melatova/PlantHabitatMonitor/docs/hurricane_vase_cross_section.png

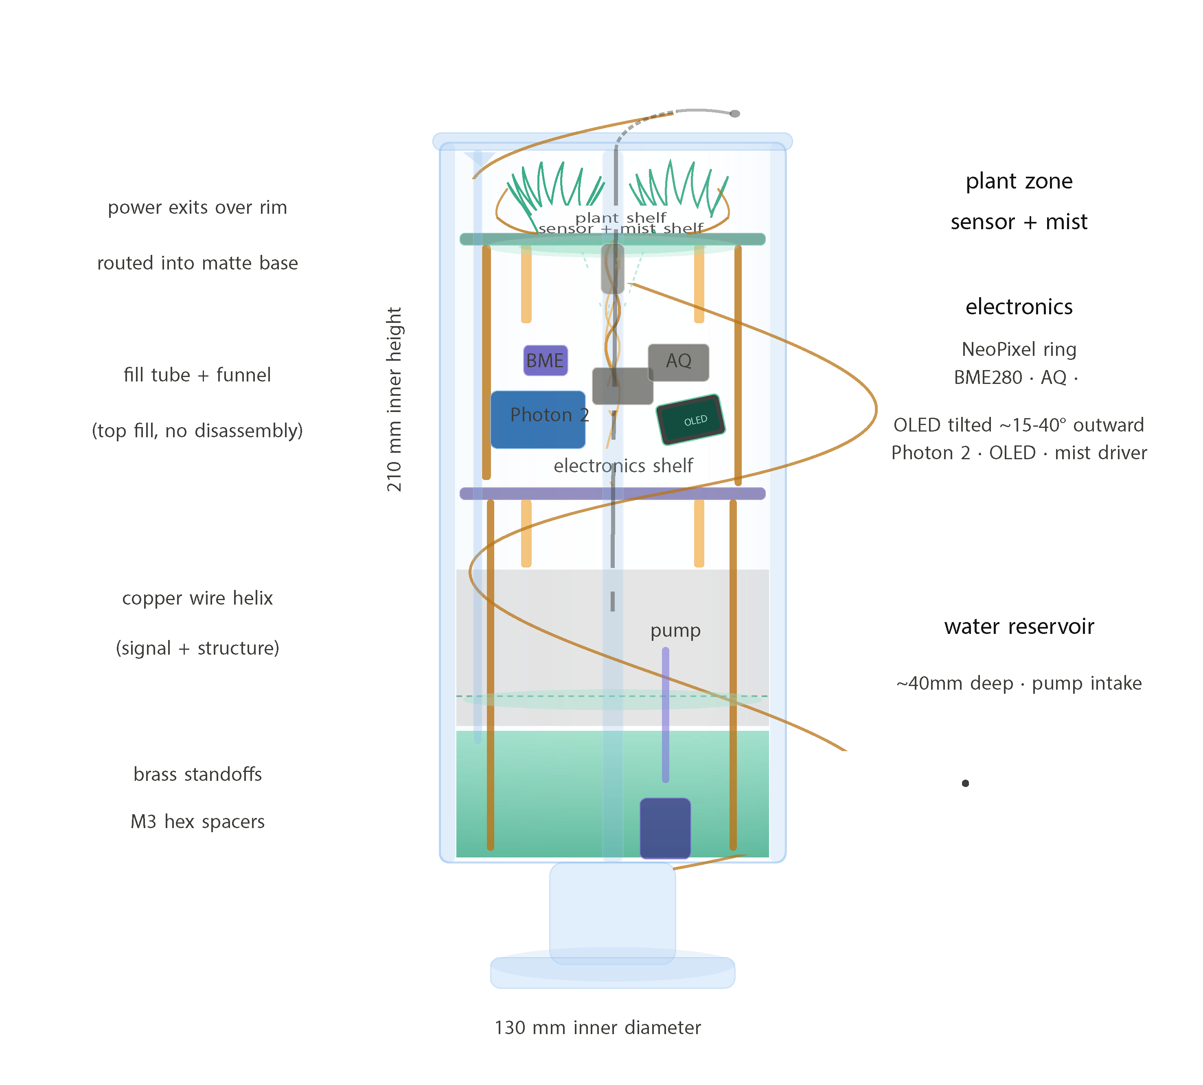
docs/hurricane_vase_cross_section.png
