melatova/PlantHabitatMonitor/docs/plantMonitorFritz_bb.png

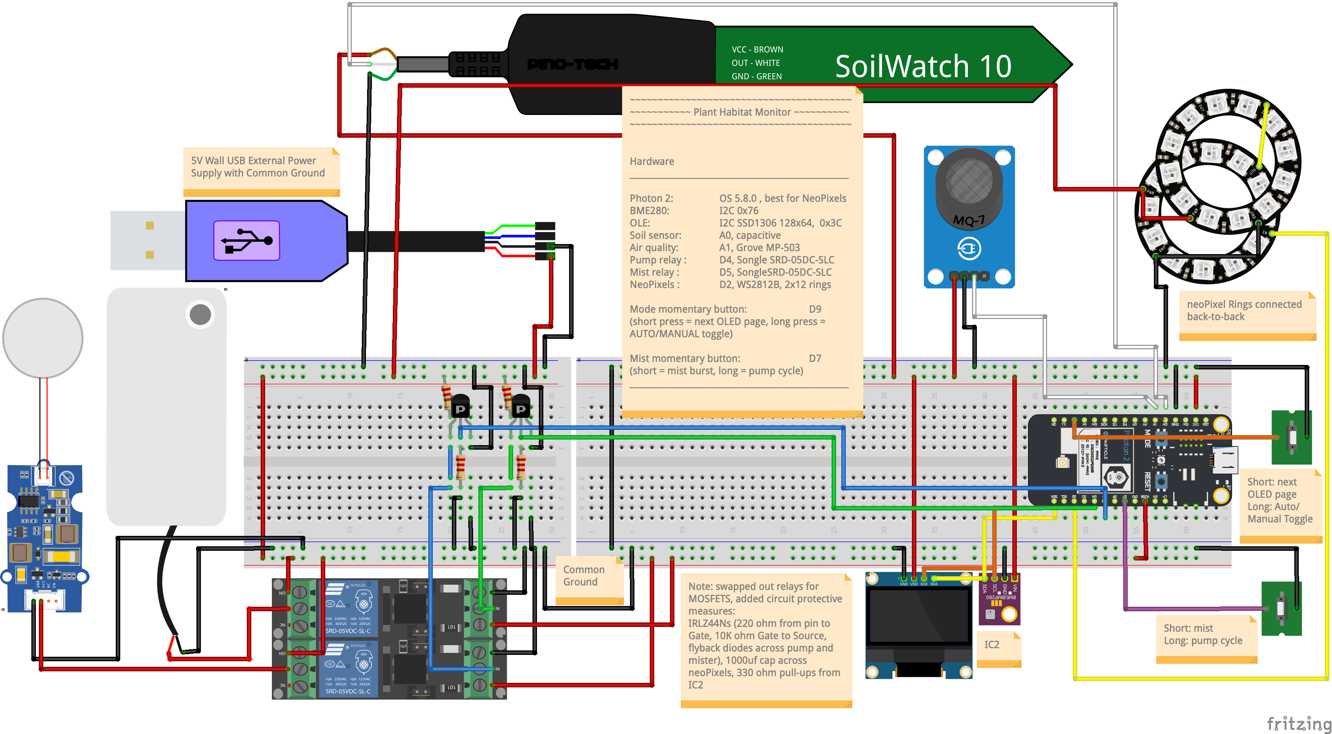
docs/plantMonitorFritz_bb.png
