melatova/PlantHabitatMonitor/docs/plantMonitorFritz_schem.png

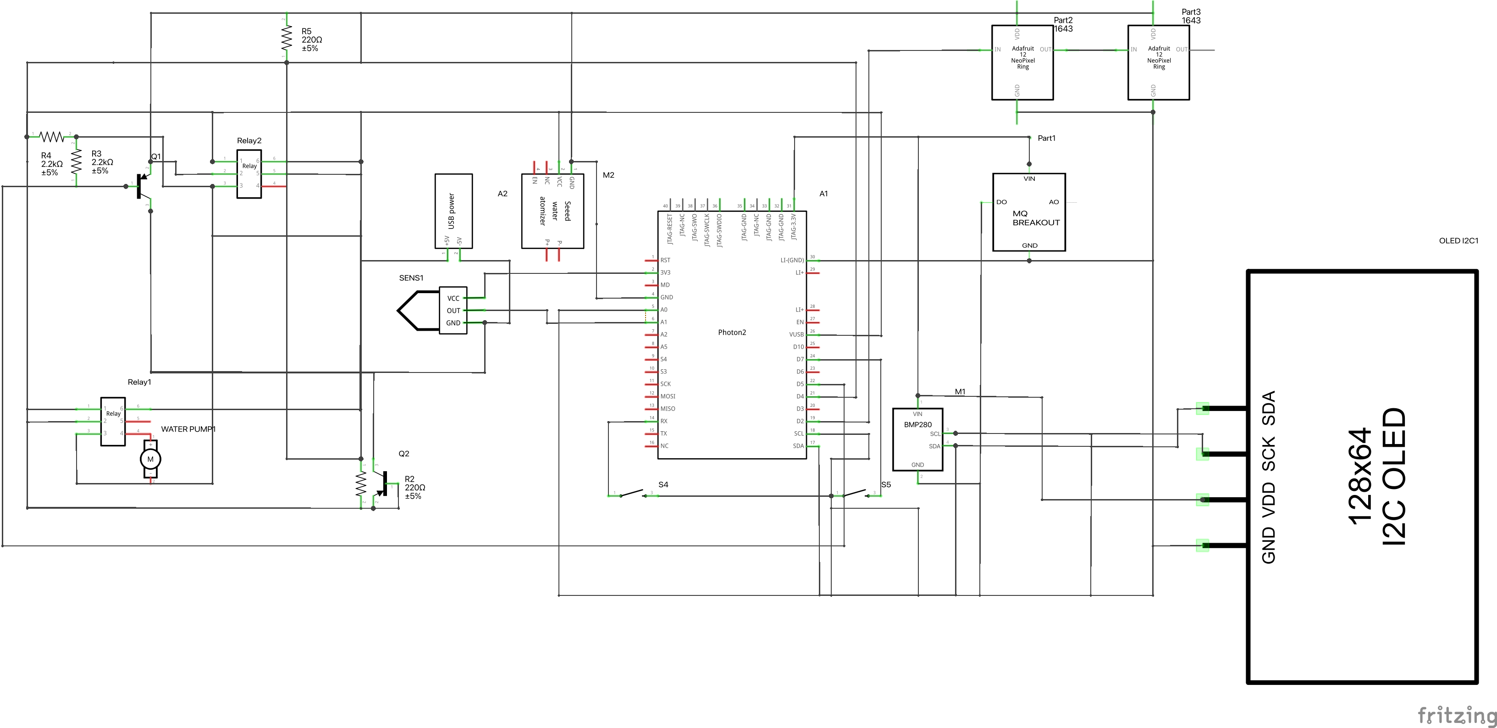
docs/plantMonitorFritz_schem.png
