melatova/PlantHabitatMonitor/images/Adafruit_Dashboard.png

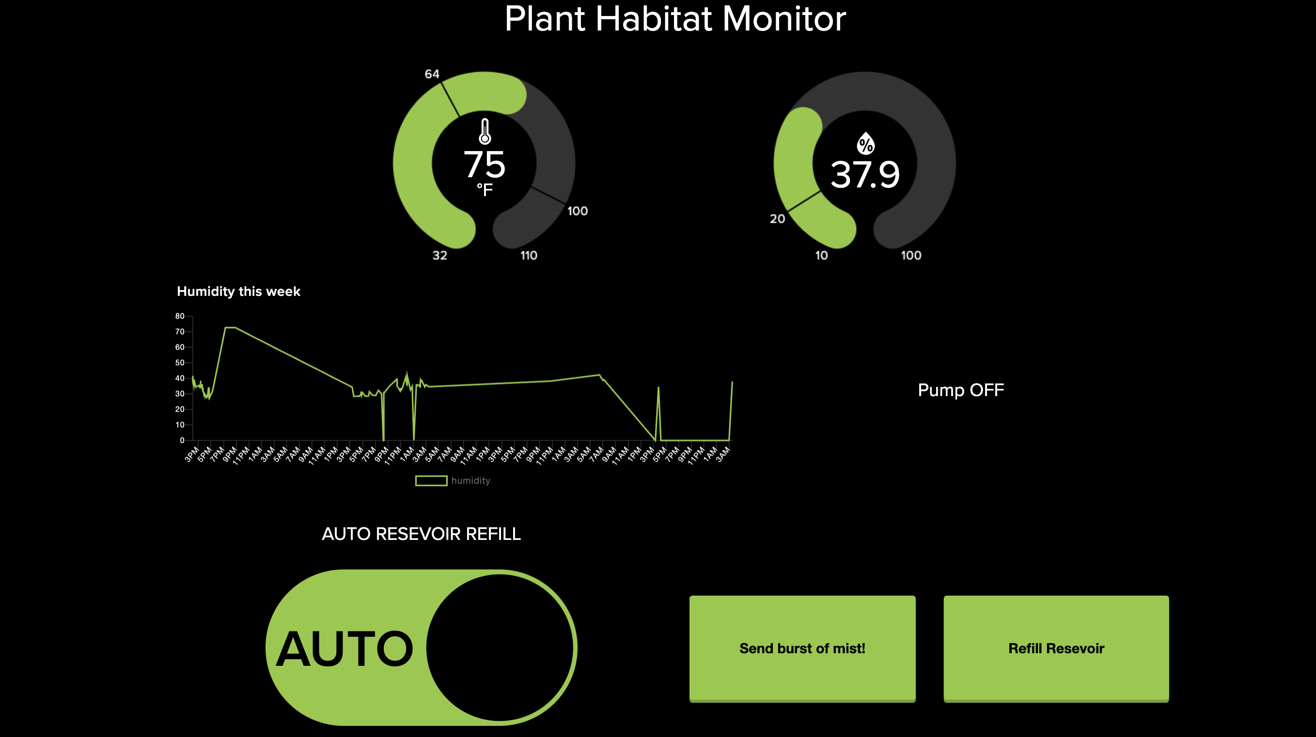
images/Adafruit_Dashboard.png
