melatova/PlantHabitatMonitor/images/Adafruit_Dashboard_Feeds.png

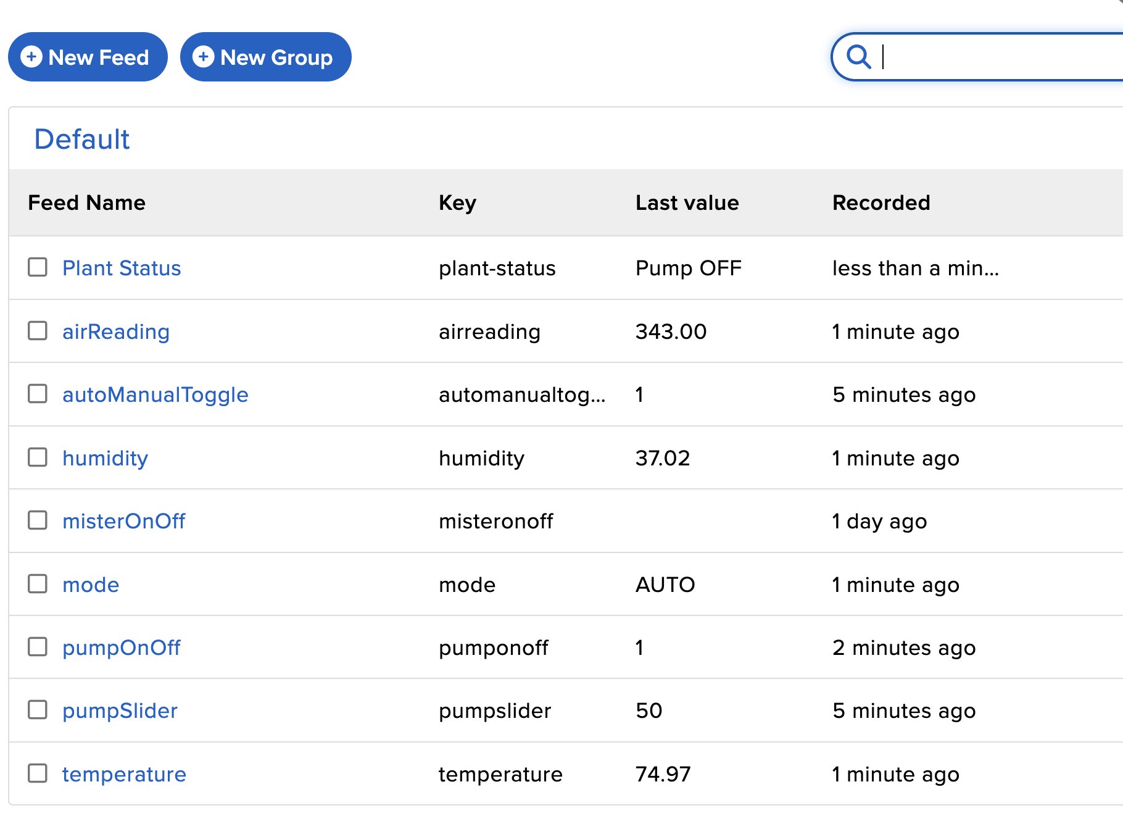
images/Adafruit_Dashboard_Feeds.png
