melatova/PlantHabitatMonitor/images/Air_plant_sanctuary_1.png

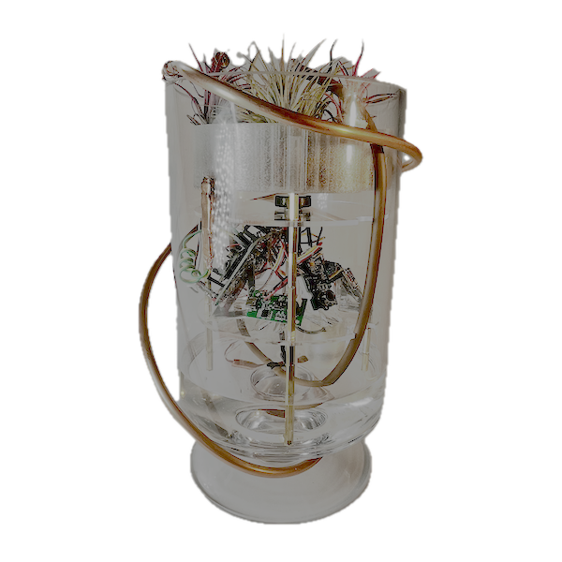
images/Air_plant_sanctuary_1.png
