melatova/PlantHabitatMonitor/images/Air_plant_sanctuary_med.gif

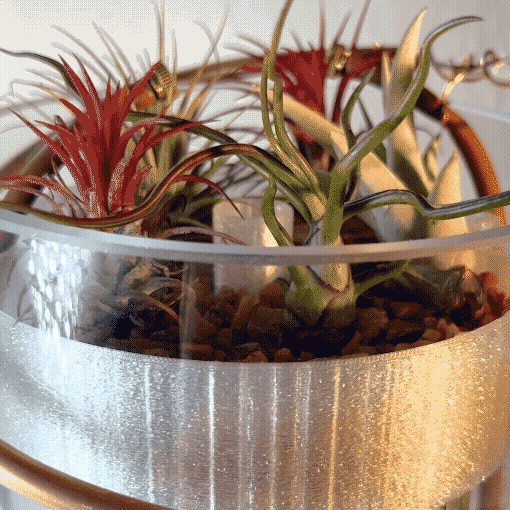
images/Air_plant_sanctuary_med.gif
