melatova/PlantHabitatMonitor/images/airplantPot_misted.png

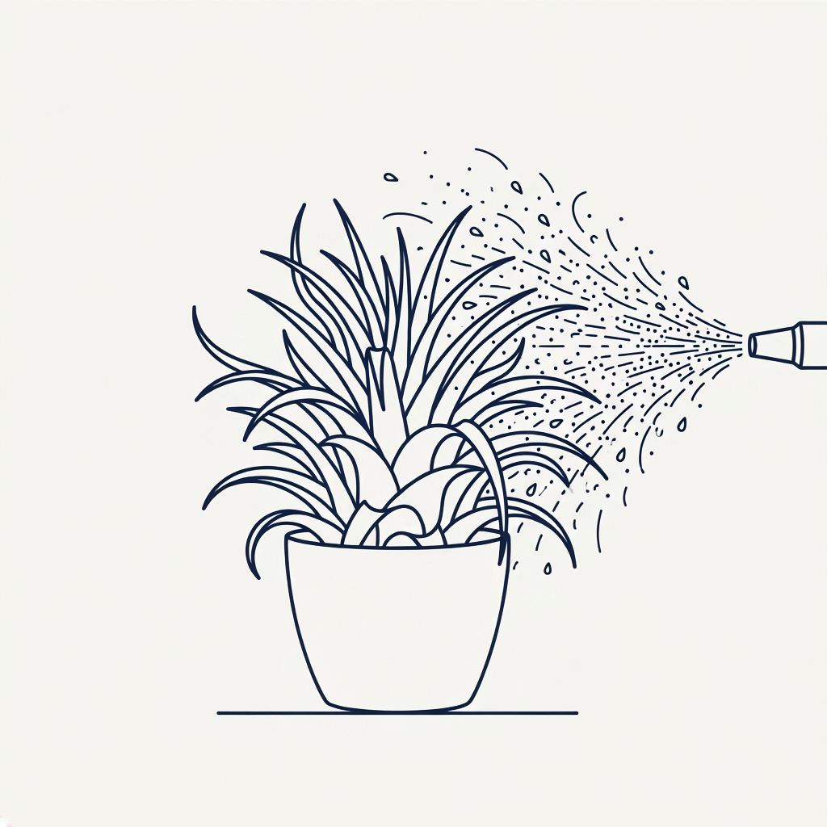
images/airplantPot_misted.png
