melatova/PlantHabitatMonitor/images/arranging_laser_cut_board_stands_sm.png

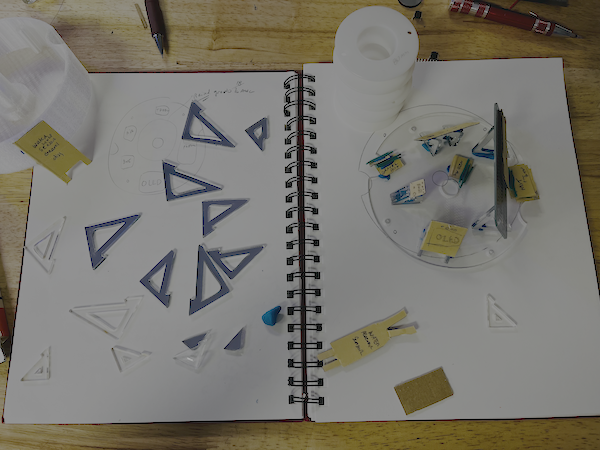
images/arranging_laser_cut_board_stands_sm.png
