melatova/PlantHabitatMonitor/images/breadboard_with_relays_sm.png

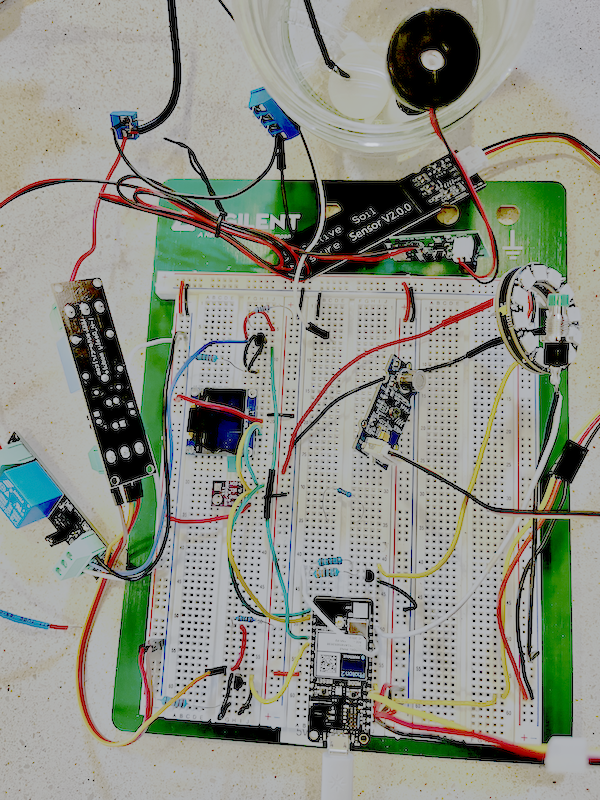
images/breadboard_with_relays_sm.png
