melatova/PlantHabitatMonitor/images/Hurricane_vase_on_snare_for_scale_sm.png

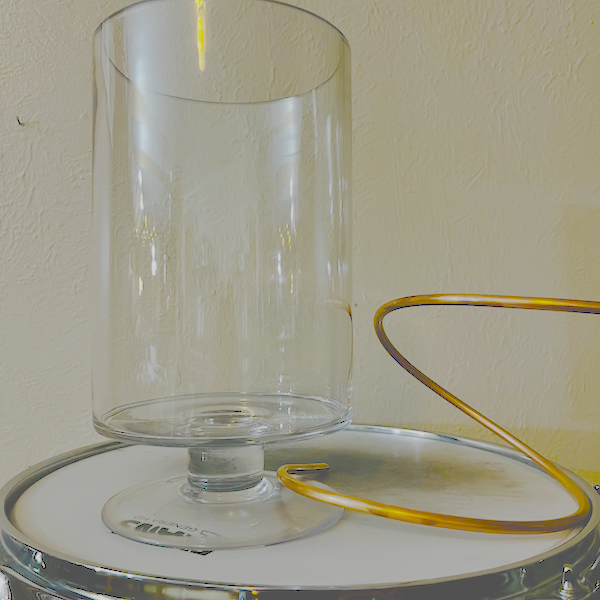
images/Hurricane_vase_on_snare_for_scale_sm.png
