melatova/PlantHabitatMonitor/images/Piezo_atomizer_board_TD-002-DIY-back.png

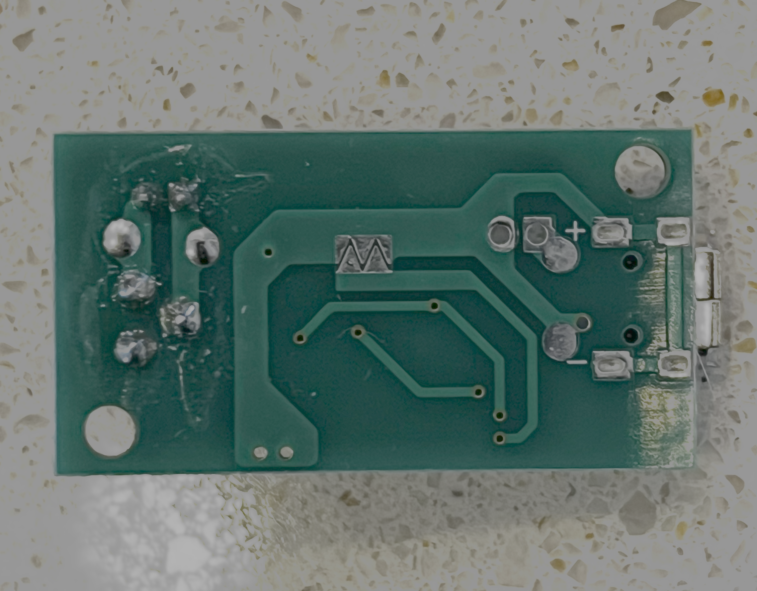
images/Piezo_atomizer_board_TD-002-DIY-back.png
