melatova/PlantHabitatMonitor/images/piezo_atomizer_magnified.png

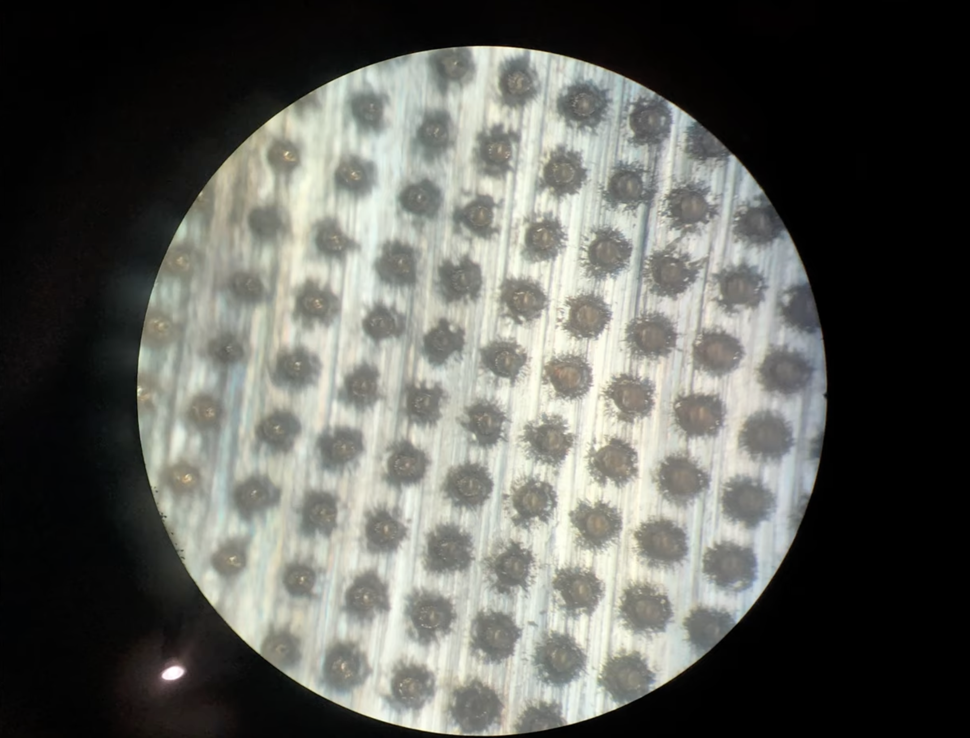
images/piezo_atomizer_magnified.png
