melatova/PlantHabitatMonitor/images/planning_circuit_layer_arrangment_sm.png

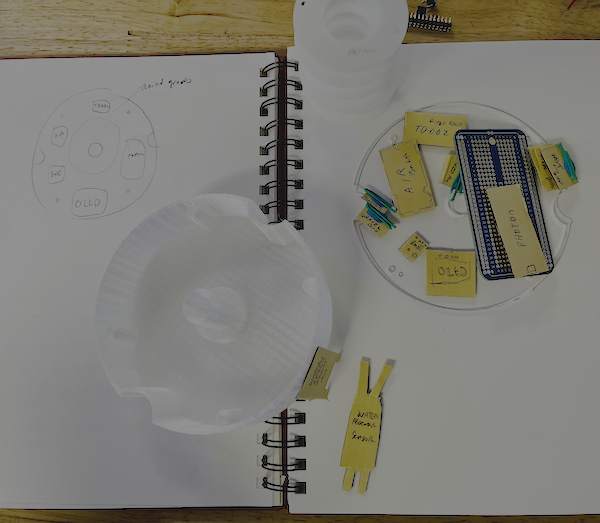
images/planning_circuit_layer_arrangment_sm.png
