melatova/PlantHabitatMonitor/images/PlantHabitatMonitor01.png

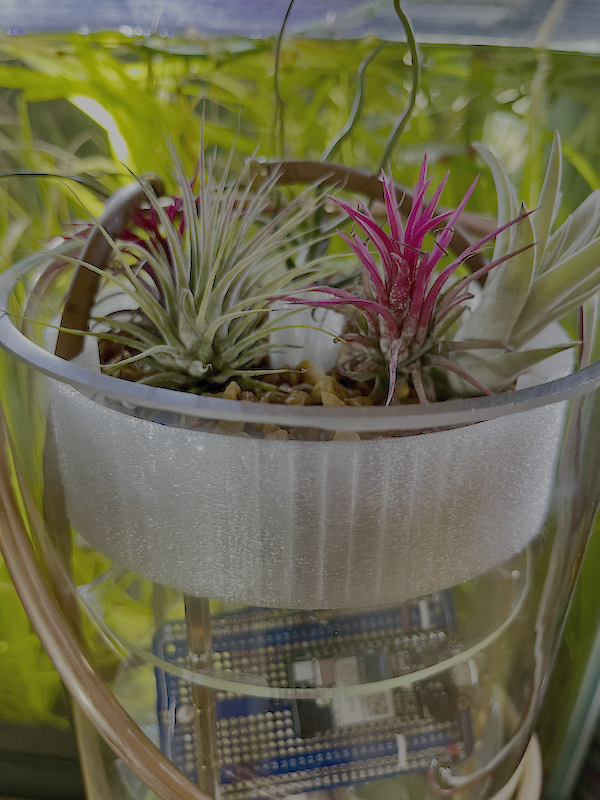
images/PlantHabitatMonitor01.png
