melatova/PlantHabitatMonitor/images/PlantHabitatMonitor02.png

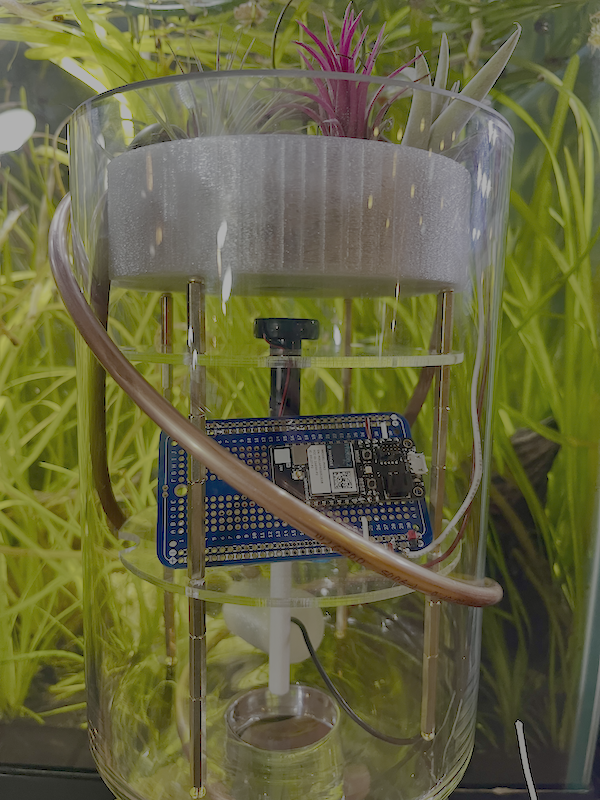
images/PlantHabitatMonitor02.png
