melatova/PlantHabitatMonitor/images/PlantHabitatMonitor03.png

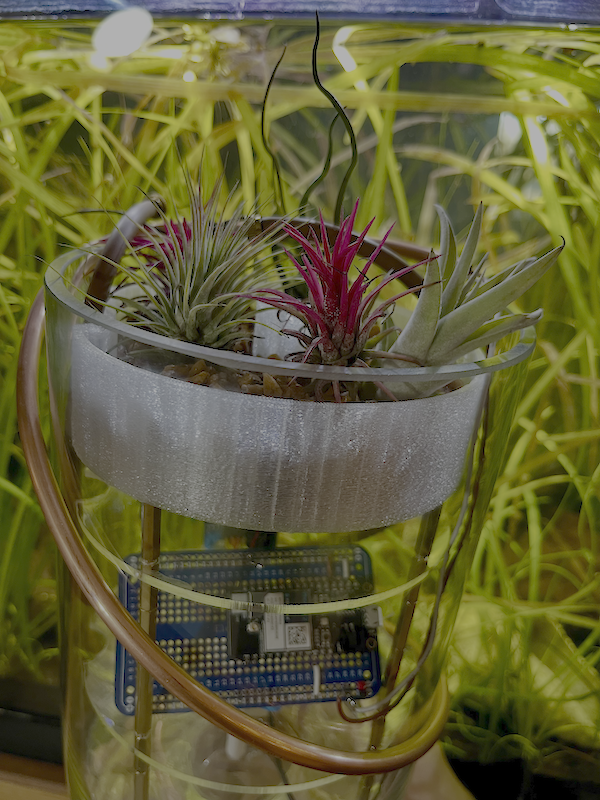
images/PlantHabitatMonitor03.png
