melatova/PlantHabitatMonitor/images/PlantHabitatMonitor04.png

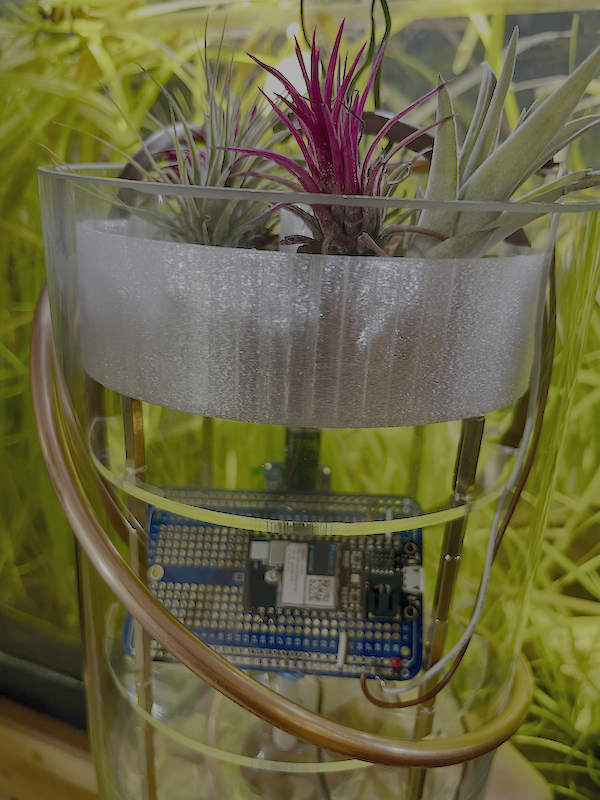
images/PlantHabitatMonitor04.png
