melatova/PlantHabitatMonitor/images/Zapier_webhook_Particle_Console.png

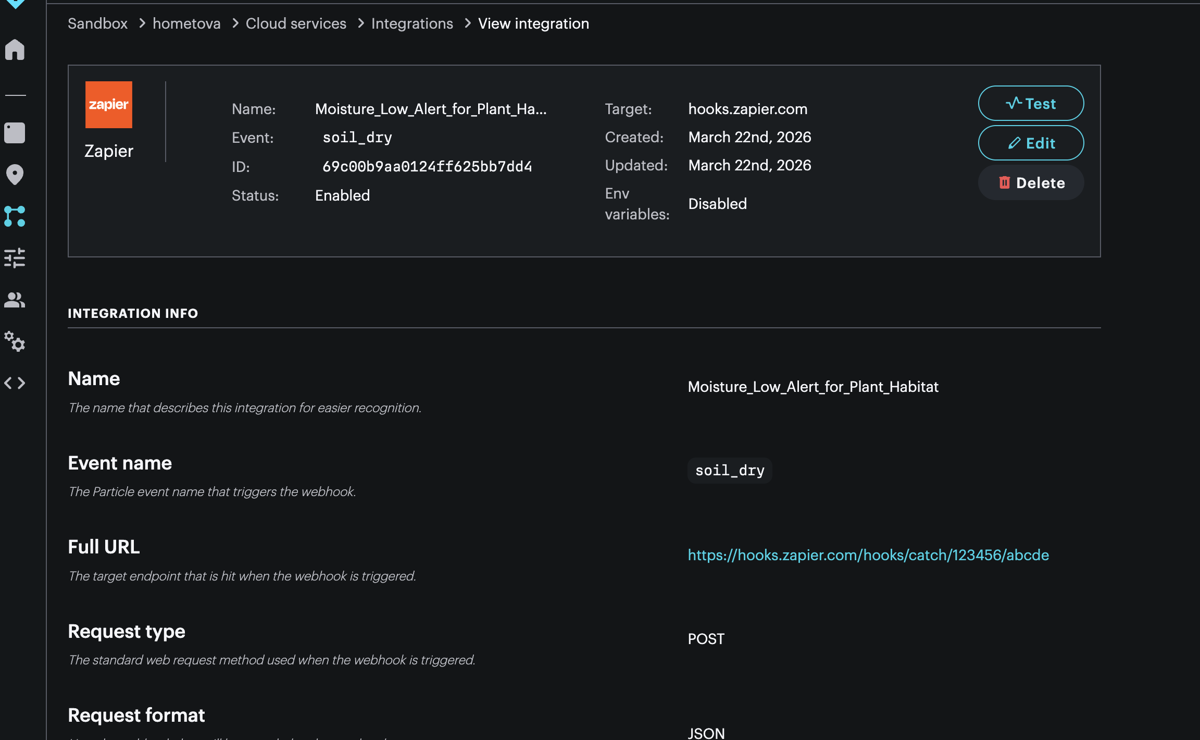
images/Zapier_webhook_Particle_Console.png
