melatova/PlantHabitatMonitor/src/gfxDisplay.h

 /*
 * Project: gfxDisplay.h
 * Description: Header file for graphics bitmaps 
 * to be used on the OLED display in the Plant Habitat Monitor project.
 * Author: Nicole
 * Date: 03/22/2026
 * 
 * Currently working on creating bitmaps for the OLED display. 
 * Thanks to Claude for guidance!
 */

#ifndef _GRAPHICS_H_
#define _GRAPHICS_H_

//graphics for using on the OLED display.

//40x40 pixel bitmap of RH% icon
const unsigned char BITMAP_RH_PERCENT[] = {
  0xFF,0xFF,0xE7,0xFF,0xFF,
  0xFF,0xFF,0xC3,0xFF,0xFF,
  0xFF,0xFF,0xC3,0xFF,0xFF,
  0xFF,0xFF,0x81,0xFF,0xFF,
  0xFF,0xFF,0x18,0xFF,0xFF,
  0xFF,0xFF,0x18,0xFF,0xFF,
  0xFF,0xFE,0x3C,0x7F,0xFF,
  0xFF,0xFC,0x7E,0x3F,0xFF,
  0xFF,0xF8,0xFF,0x1F,0xFF,
  0xFF,0xF8,0xFF,0x1F,0xFF,
  0xFF,0xF1,0xFF,0x8F,0xFF,
  0xFF,0xE3,0xFF,0xC7,0xFF,
  0xFF,0xC7,0xFF,0xE3,0xFF,
  0xFF,0xC7,0xFF,0xE3,0xFF,
  0xFF,0x8F,0xFF,0xF1,0xFF,
  0xFF,0x1C,0x3F,0xF8,0xFF,
  0xFF,0x18,0x1F,0xF8,0xFF,
  0xFE,0x38,0x0F,0xFC,0x7F,
  0xFE,0x79,0x8F,0x9E,0x7F,
  0xFC,0x79,0x8F,0x1E,0x3F,
  0xFC,0xF8,0x0E,0x3F,0x3F,
  0xF8,0xFC,0x1C,0x7F,0x1F,
  0xF8,0xFF,0xF8,0xFF,0x1F,
  0xF8,0xFF,0xF1,0xFF,0x1F,
  0xF8,0xFF,0xE3,0xFF,0x1F,
  0xF8,0xFF,0xC7,0xFF,0x1F,
  0xF8,0xFF,0x8F,0xFF,0x1F,
  0xF8,0xFF,0x1F,0xFF,0x1F,
  0xF8,0xFE,0x38,0x3F,0x1F,
  0xFC,0xFC,0x70,0x1F,0x3F,
  0xFC,0x78,0xF1,0x9E,0x3F,
  0xFE,0x79,0xF1,0x9E,0x7F,
  0xFE,0x3F,0xF0,0x1C,0x7F,
  0xFF,0x1F,0xF8,0x18,0xFF,
  0xFF,0x0F,0xFC,0x30,0xFF,
  0xFF,0x87,0xFF,0xE1,0xFF,
  0xFF,0xC1,0xFF,0x83,0xFF,
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
  0xF8,0x3F,0xFF,0xFC,0x1F,
  0xFC,0x0F,0xFF,0xF0,0x3F,
  0xFE,0x07,0xFF,0xE0,0x7F,
  0xFF,0x00,0xFF,0x00,0xFF,
  0xFF,0x80,0x00,0x01,0xFF,
  0xFF,0xE0,0x00,0x03,0xFF,
  0xFF,0xF8,0x00,0x0F,0xFF,
  0xFF,0xFE,0x00,0x7F,0xFF,
  0xFF,0xFF,0xFF,0xFF,0xFF
};

#endif // _GRAPHICS_H_
